heli2src/Epaper_Mqtt/color_setup.py

# Released under the MIT license see LICENSE
# Thanks to @Peter for a great micropython-nano-gui: https://github.com/peterhinch/micropython-nano-gui

# Demo of initialisation procedure designed to minimise risk of memory fail
# when instantiating the frame buffer. The aim is to do this as early as
# possible before importing other modules.

# -----------------------------------------------------------------------------
# * | File        :	  color_setup.py
# * | Function    :   configuration file
# * | This version:   V1.2
# * | Date        :   2022-10-11
# -----------------------------------------------------------------------------

import machine
import gc

## For Pico-ePaper-2.13
# from drivers.ePaper2in13V3 import EPD as SSD

## For Pico-ePaper-2.13_V4
# from drivers.ePaper2in13V4 import EPD as SSD

# For Pico-ePaper-2.13-B
#from drivers.ePaper2in13bV4 import EPD as SSD
#from drivers.ePaper2in13bV4 import EPDred as SSDred

## For Pico-ePaper-2.7
# from drivers.ePaper2in7 import EPD as SSD

## For Pico-ePaper-2.7_V2
# from drivers.ePaper2in7V2 import EPD as SSD

## For Pico-ePaper-2.9
# from drivers.ePaper2in9 import EPD as SSD

## For Pico-ePaper-3.7
# from drivers.ePaper3in7 import EPD as SSD

## For Pico-ePaper-4.2
# from drivers.ePaper4in2 import EPD as SSD

# For Pico-ePaper-4.2_V2
# from drivers.ePaper4in2V2 import EPD as SSD

## For Pico-ePaper-7.5-B
from lib.ePaper7in5b import EPD as SSD
from lib.ePaper7in5b import EPDred as SSDred

RST_PIN         = 12
DC_PIN          = 8
CS_PIN          = 9
BUSY_PIN        = 13

prst = machine.Pin(RST_PIN, machine.Pin.OUT)
pbusy = machine.Pin(BUSY_PIN, machine.Pin.IN, machine.Pin.PULL_DOWN)
pcs = machine.Pin(CS_PIN, machine.Pin.OUT)
spi = machine.SPI(1, baudrate=4_000_000)
pdc = machine.Pin(DC_PIN, machine.Pin.OUT)
gc.collect()  # Precaution before instantiating framebuf
landscape = False
ssd = SSD(spi, pcs, pdc, prst, pbusy, landscape=landscape, asyn=False)  # Create a display instance
ssdred = SSDred(spi, pcs, pdc, prst, pbusy, landscape=landscape)  # Cread a red display instance (just for B model)
ssd.demo_mode = False

ssdred.fill(0)
ssdred.show()
gc.collect()
