heli2src/Epaper_Mqtt/tests/openwheather.py

#  # TODO: 
#  https://openweathermap.org/current
#  https://api.openweathermap.org/data/2.5/weather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

# result = {"coord":{"lon":7.5573,"lat":47.7726},
#"weather":[{"id":804,"main":"Clouds","description":"Bedeckt","icon":"04n"}],
#"base":"stations",
#"main":{"temp":3.78,"feels_like":3.78,"temp_min":2.49,"temp_max":4.66,"pressure":1030,"humidity":88,"sea_level":1030,"grnd_level":991},
#"visibility":10000,
#"wind":{"speed":1.03,"deg":222,"gust":1.15},
#"clouds":{"all":88},
#"dt":1733343010,"sys":{"type":2,"id":2005910,"country":"DE","sunrise":1733295704,"sunset":1733326730},"timezone":3600,"id":2838534,"name":"Schliengen","cod":200}
